KadhirTheEngineer/Kaboard/mech/kea-choc-v1-choc-spaced-homing-keycap-1u.step

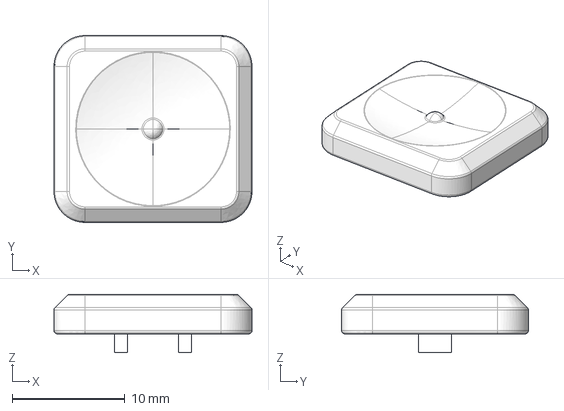
[picture p12: CAD file, 2025-09-02]
mech/kea-choc-v1-choc-spaced-homing-keycap-1u.step
17.6 x 16.6 x 5.14 mm
