KadhirTheEngineer/Kaboard/mech/Kailh Choc FunkMonk 1u.step

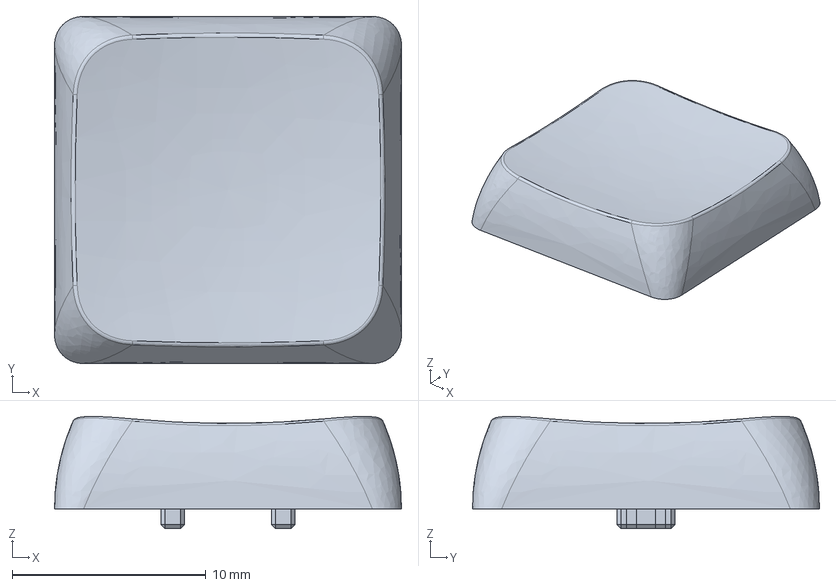
[picture p13: CAD file, 2025-09-02]
mech/Kailh Choc FunkMonk 1u.step
17.9 x 17.9 x 5.78 mm
